nawakman/bluetoothKeylogger/bluetoothKeyLoggerUS/keycodesUS.h

const uint8_t keyboardKeysUS[256]={0x0,0x0,0x0,0x0,0xce,0x0,0x81,0x85,0x80,0x84,0x82,0x86,0x83,0x0,0x0,0x0,0x0,0xd2,0xd5,0xd3,0xd6,0xd8,0xd7,0xda,0xd9,0xd1,0xd4,0xb1,0xb2,0xb3,0xb0,0x20,0xea,0xe1,0xe2,0xe3,0xe4,0xe5,0xe6,0xe7,0xe8,0xe9,0xeb,0xb0,0x2b,0x2d,0x2a,0x2f,0xea,0xe1,0xe2,0xe3,0xe4,0xe5,0xe6,0xe7,0xe8,0xe9,0x27,0x2c,0x2d,0x2e,0x2f,0x0,0x60,0x61,0x62,0x63,0x64,0x65,0x66,0x67,0x68,0x69,0x6a,0x6b,0x6c,0x6d,0x6e,0x6f,0x70,0x71,0x72,0x73,0x74,0x75,0x76,0x77,0x78,0x79,0x7a,0x3b,0x5c,0x5b,0x5d,0x3d,0x0,0xc2,0xc3,0xc4,0xc5,0xc6,0xc7,0xc8,0xc9,0xca,0xcb,0xcc,0xcd,0x0,0x0,0x0,0x0,0x0,0x0,0x0,0x0,0x0,0x0,0x0,0x0,0x0,0x0,0x0,0x0,0x0,0x0,0x0,0x0,0x0,0x0,0x0,0x0,0x0,0x0,0x0,0x0,0x0,0x0,0x0,0x0,0x0,0x0,0x0,0x0,0x0,0x0,0x0,0x0,0x0,0x0,0x0,0x0,0x0,0x0,0x0,0x0,0x0,0x0,0x0,0x0,0x0,0x0,0x0,0x0,0x0,0x0,0x0,0x0,0x0,0x0,0x0,0x0,0x0,0x0,0x0,0x0,0x0,0x0,0x0,0x0,0x0,0x0,0x0,0x0,0x0,0x0,0x0,0x0,0x0,0x0,0x0,0x0,0x0,0x0,0x0,0x0,0x0,0x0,0x0,0x0,0x0,0x0,0x0,0x0,0x0,0x0,0x0,0x0,0x0,0x0,0x0,0x0,0x0,0x0,0x0,0x0,0x0,0x0,0x0,0x0,0x0,0x0,0x0,0x0,0x0,0x0,0x0,0x0,0x0,0x0,0x0,0x0,0x0,0x0,0x0,0x0,0x0,0x0,0x0,0x0,0x0,0x0,0x0,0x0,0x0,0x0,0x0,0x0,0x0,0xc1,0x0,0x0,0x0,0x0,0x0};//for access with PS2 key as index
const uint8_t keyboardShiftKeysUS[256]={0x0,0x0,0x0,0x0,0xce,0x0,0x81,0x85,0x80,0x84,0x82,0x86,0x83,0x0,0x0,0x0,0x0,0xd2,0xd5,0xd3,0xd6,0xd8,0xd7,0xda,0xd9,0xd1,0xd4,0xb1,0xb2,0xb3,0xb0,0x20,0x0,0x0,0x0,0x0,0x0,0x0,0x0,0x0,0x0,0x0,0x0,0x0,0x0,0x0,0x0,0x0,0x29,0x21,0x1f,0x23,0x24,0x25,0x5e,0x26,0x2a,0x28,0x22,0x3c,0x5f,0x3e,0x38,0x0,0x7e,0x41,0x42,0x43,0x44,0x45,0x46,0x47,0x48,0x49,0x4a,0x4b,0x4c,0x4d,0x4e,0x4f,0x50,0x51,0x52,0x53,0x54,0x55,0x56,0x57,0x58,0x59,0x5a,0x3a,0x7c,0x7b,0x7d,0x2b,0x0,0x0,0x0,0x0,0x0,0x0,0x0,0x0,0x0,0x0,0x0,0x0,0x0,0x0,0x0,0x0,0x0,0x0,0x0,0x0,0x0,0x0,0x0,0x0,0x0,0x0,0x0,0x0,0x0,0x0,0x0,0x0,0x0,0x0,0x0,0x0,0x0,0x0,0x0,0x0,0x0,0x0,0x0,0x0,0x0,0x0,0x0,0x0,0x0,0x0,0x0,0x0,0x0,0x0,0x0,0x0,0x0,0x0,0x0,0x0,0x0,0x0,0x0,0x0,0x0,0x0,0x0,0x0,0x0,0x0,0x0,0x0,0x0,0x0,0x0,0x0,0x0,0x0,0x0,0x0,0x0,0x0,0x0,0x0,0x0,0x0,0x0,0x0,0x0,0x0,0x0,0x0,0x0,0x0,0x0,0x0,0x0,0x0,0x0,0x0,0x0,0x0,0x0,0x0,0x0,0x0,0x0,0x0,0x0,0x0,0x0,0x0,0x0,0x0,0x0,0x0,0x0,0x0,0x0,0x0,0x0,0x0,0x0,0x0,0x0,0x0,0x0,0x0,0x0,0x0,0x0,0x0,0x0,0x0,0x0,0x0,0x0,0x0,0x0,0x0,0x0,0x0,0x0,0x0,0x0,0x0,0x0,0x0,0x0,0x0,0x0,0x0,0x0,0x0,0xc1,0x0,0x0,0x0,0x0,0x0};//for access with PS2 key as index (shift pressed)
const uint8_t charactersUS[96]={'','','','','','','','','','','','','','','','','','','','','','','','','','','','','','','','','0','1','2','3','4','5','6','7','8','9','.','','+','-','*','/','0','1','2','3','4','5','6','7','8','9','\'',',','-','.','/','','`','a','b','c','d','e','f','g','h','i','j','k','l','m','n','o','p','q','r','s','t','u','v','w','x','y','z',';','\\','[',']','='};//character associated to each key
const uint8_t shiftCharactersUS[96]={'','','','','','','','','','','','','','','','','','','','','','','','','','','','','','','','','','','','','','','','','','','','','','','','',')','!','@','#','$','%','^','&','*','(','"','<','_','>','?','','~','A','B','C','D','E','F','G','H','I','J','K','L','M','N','O','P','Q','R','S','T','U','V','W','X','Y','Z',':','|','{','}','+'};//character associated to each shift key
